knack-tactical/PVS-69/Gen3 FOXTROT/STL/FOXTROT Printable Washer.stl

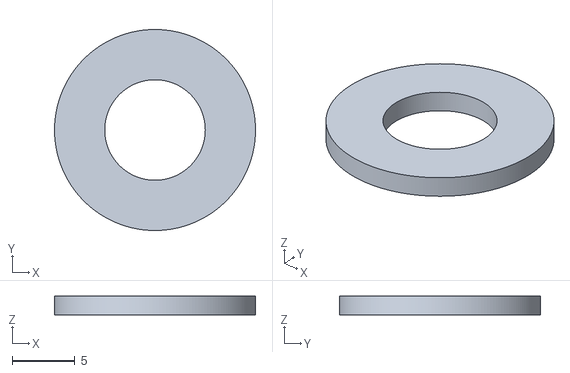
[picture p16: CAD file, 2023-03-20]
Gen3 FOXTROT/STL/FOXTROT Printable Washer.stl
16.0 x 16.0 x 1.50
