knack-tactical/PVS-69/Older Versions/__Archive/Gen3 CHARLIE/STL/+7 TIP_right.stl

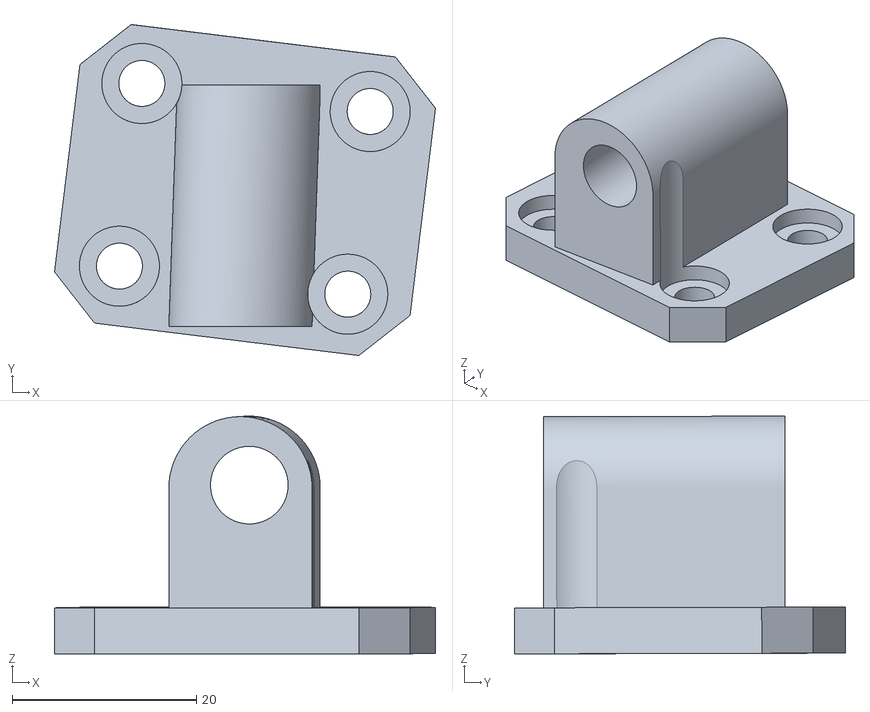
[picture p17: CAD file, 2022-10-31, an earlier design]
Older Versions/__Archive/Gen3 CHARLIE/STL/+7 TIP_right.stl
41.4 x 36.0 x 25.8
